carsonrobles/fpga-guitar-pedal/src/rtl/top.sv

`include "defaults.svh"
`include "sample_pkg.svh"

module top (
  input  wire        FPGA_CLK_100,
  input  wire        FPGA_RST_N,

  input  wire [15:0] SW,                  // switches
  output wire [15:0] LED,                 // LEDs
  output wire [ 2:0] RGB_L,               // RGB LEDs
  output wire [ 2:0] RGB_R,

  output wire        JA_MCLK_TX,          // PMOD I2S ports
  output wire        JA_LRCK_TX,
  output wire        JA_SCLK_TX,
  output wire        JA_SDO_TX,
  output wire        JA_MCLK_RX,
  output wire        JA_LRCK_RX,
  output wire        JA_SCLK_RX,
  input  wire        JA_SDI_RX
);


  wire mclk;

  mclk_gen mclk_gen_i (
    .clk  (FPGA_CLK_100),
    .rst  (~FPGA_RST_N),
    .mclk (mclk)
  );


  // synchronize external reset button to mclk domain
  wire rst;

  sync #(
    .NUM_FF     (2),
    .INIT_VALUE (0)
  ) sync_rst_i (
    .clk   (mclk),
    .rst   (0),
    .sig_i (~FPGA_RST_N),
    .sig_o (rst)
  );


  wire lrck;
  wire sclk;

  sample_pkg::sample_t rx_data;
  wire                 rx_vld;
  sample_pkg::sample_t tx_data;
  wire                 tx_vld;

  // i2s communication
  i2s i2s_i (
    .mclk    (mclk),
    .rst     (rst),
    .rx_data (rx_data),
    .rx_vld  (rx_vld),
    .tx_data (tx_data),
    .tx_vld  (tx_vld),
    .lrck    (lrck),
    .sclk    (sclk),
    .sdi     (JA_SDI_RX),
    .sdo     (JA_SDO_TX)
  );

  // assign PMOD clock outputs
  assign JA_MCLK_TX = mclk;
  assign JA_LRCK_TX = lrck;
  assign JA_SCLK_TX = sclk;
  assign JA_MCLK_RX = mclk;
  assign JA_LRCK_RX = lrck;
  assign JA_SCLK_RX = sclk;


  wire eff_en = 1;

  // effects pipe
  eff_pipe eff_pipe_i (
    .clk    (mclk),
    .rst    (rst),
    .en     (eff_en),
    .sel    (SW),
    .data_i (rx_data),
    .vld_i  (rx_vld),
    .data_o (tx_data),
    .vld_o  (tx_vld)
  );


  // leds follow switches
  assign LED = SW;

  // heartbeat LEDs
  rgb_drv rgb_drv_l_i (
    .clk  (FPGA_CLK_100),
    .rst  (~FPGA_RST_N),
    .mode (1),
    .red  (RGB_L[0]),
    .grn  (RGB_L[1]),
    .blu  (RGB_L[2])
  );

  assign RGB_R[0] = 0;
  assign RGB_R[1] = 0;
  assign RGB_R[2] = ~RGB_L[2];


endmodule
