carsonrobles/fpga-guitar-pedal/src/rtl/nco/cos_lut.sv

`include "defaults.svh"


module cos_lut #(
  parameter     FILE_NAME = "/home/carson/poly/fpga-guitar-pedal/fab/data/lut.hex",
  parameter int WIDTH     = 24,
  parameter int DEPTH     = 256
) (
  input  wire                      clk,
  input  wire                      rst,

  input  wire  [$clog2(DEPTH)-1:0] phi,

  output logic [        WIDTH-1:0] wav
);


  logic [WIDTH-1:0] lut [DEPTH];

  initial begin
    // read sinusoid data file into lut
    $readmemh(FILE_NAME, lut);
  end


  always_comb wav = lut[phi];


endmodule
