carsonrobles/fpga-guitar-pedal/src/ip/clk_wiz_ip/clk_wiz_ip_sim_netlist.v

// Copyright 1986-2018 Xilinx, Inc. All Rights Reserved.
// --------------------------------------------------------------------------------
// Tool Version: Vivado v.2018.3 (lin64) Build 2405991 Thu Dec  6 23:36:41 MST 2018
// Date        : Wed Apr 24 12:31:04 2019
// Host        : ubuntu running 64-bit Ubuntu 18.04.1 LTS
// Command     : write_verilog -force -mode funcsim
//               /home/carson/poly/fpga-guitar-pedal/src/ip/clk_wiz_ip/clk_wiz_ip_sim_netlist.v
// Design      : clk_wiz_ip
// Purpose     : This verilog netlist is a functional simulation representation of the design and should not be modified
//               or synthesized. This netlist cannot be used for SDF annotated simulation.
// Device      : xc7a100tcsg324-1
// --------------------------------------------------------------------------------
`timescale 1 ps / 1 ps

(* NotValidForBitStream *)
module clk_wiz_ip
   (clk_o,
    reset,
    locked,
    clk_i);
  output clk_o;
  input reset;
  output locked;
  input clk_i;

  (* IBUF_LOW_PWR *) wire clk_i;
  wire clk_o;
  wire locked;
  wire reset;

  clk_wiz_ip_clk_wiz_ip_clk_wiz inst
       (.clk_i(clk_i),
        .clk_o(clk_o),
        .locked(locked),
        .reset(reset));
endmodule

(* ORIG_REF_NAME = "clk_wiz_ip_clk_wiz" *) 
module clk_wiz_ip_clk_wiz_ip_clk_wiz
   (clk_o,
    reset,
    locked,
    clk_i);
  output clk_o;
  input reset;
  output locked;
  input clk_i;

  wire clk_i;
  wire clk_i_clk_wiz_ip;
  wire clk_o;
  wire clk_o_clk_wiz_ip;
  wire clkfbout_buf_clk_wiz_ip;
  wire clkfbout_clk_wiz_ip;
  wire locked;
  wire reset;
  wire NLW_plle2_adv_inst_CLKOUT1_UNCONNECTED;
  wire NLW_plle2_adv_inst_CLKOUT2_UNCONNECTED;
  wire NLW_plle2_adv_inst_CLKOUT3_UNCONNECTED;
  wire NLW_plle2_adv_inst_CLKOUT4_UNCONNECTED;
  wire NLW_plle2_adv_inst_CLKOUT5_UNCONNECTED;
  wire NLW_plle2_adv_inst_DRDY_UNCONNECTED;
  wire [15:0]NLW_plle2_adv_inst_DO_UNCONNECTED;

  (* BOX_TYPE = "PRIMITIVE" *) 
  BUFG clkf_buf
       (.I(clkfbout_clk_wiz_ip),
        .O(clkfbout_buf_clk_wiz_ip));
  (* BOX_TYPE = "PRIMITIVE" *) 
  (* CAPACITANCE = "DONT_CARE" *) 
  (* IBUF_DELAY_VALUE = "0" *) 
  (* IFD_DELAY_VALUE = "AUTO" *) 
  IBUF #(
    .IOSTANDARD("DEFAULT")) 
    clkin1_ibufg
       (.I(clk_i),
        .O(clk_i_clk_wiz_ip));
  (* BOX_TYPE = "PRIMITIVE" *) 
  BUFG clkout1_buf
       (.I(clk_o_clk_wiz_ip),
        .O(clk_o));
  (* BOX_TYPE = "PRIMITIVE" *) 
  PLLE2_ADV #(
    .BANDWIDTH("OPTIMIZED"),
    .CLKFBOUT_MULT(14),
    .CLKFBOUT_PHASE(0.000000),
    .CLKIN1_PERIOD(10.000000),
    .CLKIN2_PERIOD(0.000000),
    .CLKOUT0_DIVIDE(62),
    .CLKOUT0_DUTY_CYCLE(0.500000),
    .CLKOUT0_PHASE(0.000000),
    .CLKOUT1_DIVIDE(1),
    .CLKOUT1_DUTY_CYCLE(0.500000),
    .CLKOUT1_PHASE(0.000000),
    .CLKOUT2_DIVIDE(1),
    .CLKOUT2_DUTY_CYCLE(0.500000),
    .CLKOUT2_PHASE(0.000000),
    .CLKOUT3_DIVIDE(1),
    .CLKOUT3_DUTY_CYCLE(0.500000),
    .CLKOUT3_PHASE(0.000000),
    .CLKOUT4_DIVIDE(1),
    .CLKOUT4_DUTY_CYCLE(0.500000),
    .CLKOUT4_PHASE(0.000000),
    .CLKOUT5_DIVIDE(1),
    .CLKOUT5_DUTY_CYCLE(0.500000),
    .CLKOUT5_PHASE(0.000000),
    .COMPENSATION("ZHOLD"),
    .DIVCLK_DIVIDE(1),
    .IS_CLKINSEL_INVERTED(1'b0),
    .IS_PWRDWN_INVERTED(1'b0),
    .IS_RST_INVERTED(1'b0),
    .REF_JITTER1(0.010000),
    .REF_JITTER2(0.010000),
    .STARTUP_WAIT("FALSE")) 
    plle2_adv_inst
       (.CLKFBIN(clkfbout_buf_clk_wiz_ip),
        .CLKFBOUT(clkfbout_clk_wiz_ip),
        .CLKIN1(clk_i_clk_wiz_ip),
        .CLKIN2(1'b0),
        .CLKINSEL(1'b1),
        .CLKOUT0(clk_o_clk_wiz_ip),
        .CLKOUT1(NLW_plle2_adv_inst_CLKOUT1_UNCONNECTED),
        .CLKOUT2(NLW_plle2_adv_inst_CLKOUT2_UNCONNECTED),
        .CLKOUT3(NLW_plle2_adv_inst_CLKOUT3_UNCONNECTED),
        .CLKOUT4(NLW_plle2_adv_inst_CLKOUT4_UNCONNECTED),
        .CLKOUT5(NLW_plle2_adv_inst_CLKOUT5_UNCONNECTED),
        .DADDR({1'b0,1'b0,1'b0,1'b0,1'b0,1'b0,1'b0}),
        .DCLK(1'b0),
        .DEN(1'b0),
        .DI({1'b0,1'b0,1'b0,1'b0,1'b0,1'b0,1'b0,1'b0,1'b0,1'b0,1'b0,1'b0,1'b0,1'b0,1'b0,1'b0}),
        .DO(NLW_plle2_adv_inst_DO_UNCONNECTED[15:0]),
        .DRDY(NLW_plle2_adv_inst_DRDY_UNCONNECTED),
        .DWE(1'b0),
        .LOCKED(locked),
        .PWRDWN(1'b0),
        .RST(reset));
endmodule
`ifndef GLBL
`define GLBL
`timescale  1 ps / 1 ps

module glbl ();

    parameter ROC_WIDTH = 100000;
    parameter TOC_WIDTH = 0;

//--------   STARTUP Globals --------------
    wire GSR;
    wire GTS;
    wire GWE;
    wire PRLD;
    tri1 p_up_tmp;
    tri (weak1, strong0) PLL_LOCKG = p_up_tmp;

    wire PROGB_GLBL;
    wire CCLKO_GLBL;
    wire FCSBO_GLBL;
    wire [3:0] DO_GLBL;
    wire [3:0] DI_GLBL;
   
    reg GSR_int;
    reg GTS_int;
    reg PRLD_int;

//--------   JTAG Globals --------------
    wire JTAG_TDO_GLBL;
    wire JTAG_TCK_GLBL;
    wire JTAG_TDI_GLBL;
    wire JTAG_TMS_GLBL;
    wire JTAG_TRST_GLBL;

    reg JTAG_CAPTURE_GLBL;
    reg JTAG_RESET_GLBL;
    reg JTAG_SHIFT_GLBL;
    reg JTAG_UPDATE_GLBL;
    reg JTAG_RUNTEST_GLBL;

    reg JTAG_SEL1_GLBL = 0;
    reg JTAG_SEL2_GLBL = 0 ;
    reg JTAG_SEL3_GLBL = 0;
    reg JTAG_SEL4_GLBL = 0;

    reg JTAG_USER_TDO1_GLBL = 1'bz;
    reg JTAG_USER_TDO2_GLBL = 1'bz;
    reg JTAG_USER_TDO3_GLBL = 1'bz;
    reg JTAG_USER_TDO4_GLBL = 1'bz;

    assign (strong1, weak0) GSR = GSR_int;
    assign (strong1, weak0) GTS = GTS_int;
    assign (weak1, weak0) PRLD = PRLD_int;

    initial begin
	GSR_int = 1'b1;
	PRLD_int = 1'b1;
	#(ROC_WIDTH)
	GSR_int = 1'b0;
	PRLD_int = 1'b0;
    end

    initial begin
	GTS_int = 1'b1;
	#(TOC_WIDTH)
	GTS_int = 1'b0;
    end

endmodule
`endif
