carsonrobles/fpga-guitar-pedal/src/ip/clk_wiz_ip/clk_wiz_ip_sim_netlist.vhdl

-- Copyright 1986-2018 Xilinx, Inc. All Rights Reserved.
-- --------------------------------------------------------------------------------
-- Tool Version: Vivado v.2018.3 (lin64) Build 2405991 Thu Dec  6 23:36:41 MST 2018
-- Date        : Wed Apr 24 12:31:04 2019
-- Host        : ubuntu running 64-bit Ubuntu 18.04.1 LTS
-- Command     : write_vhdl -force -mode funcsim
--               /home/carson/poly/fpga-guitar-pedal/src/ip/clk_wiz_ip/clk_wiz_ip_sim_netlist.vhdl
-- Design      : clk_wiz_ip
-- Purpose     : This VHDL netlist is a functional simulation representation of the design and should not be modified or
--               synthesized. This netlist cannot be used for SDF annotated simulation.
-- Device      : xc7a100tcsg324-1
-- --------------------------------------------------------------------------------
library IEEE;
use IEEE.STD_LOGIC_1164.ALL;
library UNISIM;
use UNISIM.VCOMPONENTS.ALL;
entity clk_wiz_ip_clk_wiz_ip_clk_wiz is
  port (
    clk_o : out STD_LOGIC;
    reset : in STD_LOGIC;
    locked : out STD_LOGIC;
    clk_i : in STD_LOGIC
  );
  attribute ORIG_REF_NAME : string;
  attribute ORIG_REF_NAME of clk_wiz_ip_clk_wiz_ip_clk_wiz : entity is "clk_wiz_ip_clk_wiz";
end clk_wiz_ip_clk_wiz_ip_clk_wiz;

architecture STRUCTURE of clk_wiz_ip_clk_wiz_ip_clk_wiz is
  signal clk_i_clk_wiz_ip : STD_LOGIC;
  signal clk_o_clk_wiz_ip : STD_LOGIC;
  signal clkfbout_buf_clk_wiz_ip : STD_LOGIC;
  signal clkfbout_clk_wiz_ip : STD_LOGIC;
  signal NLW_plle2_adv_inst_CLKOUT1_UNCONNECTED : STD_LOGIC;
  signal NLW_plle2_adv_inst_CLKOUT2_UNCONNECTED : STD_LOGIC;
  signal NLW_plle2_adv_inst_CLKOUT3_UNCONNECTED : STD_LOGIC;
  signal NLW_plle2_adv_inst_CLKOUT4_UNCONNECTED : STD_LOGIC;
  signal NLW_plle2_adv_inst_CLKOUT5_UNCONNECTED : STD_LOGIC;
  signal NLW_plle2_adv_inst_DRDY_UNCONNECTED : STD_LOGIC;
  signal NLW_plle2_adv_inst_DO_UNCONNECTED : STD_LOGIC_VECTOR ( 15 downto 0 );
  attribute BOX_TYPE : string;
  attribute BOX_TYPE of clkf_buf : label is "PRIMITIVE";
  attribute BOX_TYPE of clkin1_ibufg : label is "PRIMITIVE";
  attribute CAPACITANCE : string;
  attribute CAPACITANCE of clkin1_ibufg : label is "DONT_CARE";
  attribute IBUF_DELAY_VALUE : string;
  attribute IBUF_DELAY_VALUE of clkin1_ibufg : label is "0";
  attribute IFD_DELAY_VALUE : string;
  attribute IFD_DELAY_VALUE of clkin1_ibufg : label is "AUTO";
  attribute BOX_TYPE of clkout1_buf : label is "PRIMITIVE";
  attribute BOX_TYPE of plle2_adv_inst : label is "PRIMITIVE";
begin
clkf_buf: unisim.vcomponents.BUFG
     port map (
      I => clkfbout_clk_wiz_ip,
      O => clkfbout_buf_clk_wiz_ip
    );
clkin1_ibufg: unisim.vcomponents.IBUF
    generic map(
      IOSTANDARD => "DEFAULT"
    )
        port map (
      I => clk_i,
      O => clk_i_clk_wiz_ip
    );
clkout1_buf: unisim.vcomponents.BUFG
     port map (
      I => clk_o_clk_wiz_ip,
      O => clk_o
    );
plle2_adv_inst: unisim.vcomponents.PLLE2_ADV
    generic map(
      BANDWIDTH => "OPTIMIZED",
      CLKFBOUT_MULT => 14,
      CLKFBOUT_PHASE => 0.000000,
      CLKIN1_PERIOD => 10.000000,
      CLKIN2_PERIOD => 0.000000,
      CLKOUT0_DIVIDE => 62,
      CLKOUT0_DUTY_CYCLE => 0.500000,
      CLKOUT0_PHASE => 0.000000,
      CLKOUT1_DIVIDE => 1,
      CLKOUT1_DUTY_CYCLE => 0.500000,
      CLKOUT1_PHASE => 0.000000,
      CLKOUT2_DIVIDE => 1,
      CLKOUT2_DUTY_CYCLE => 0.500000,
      CLKOUT2_PHASE => 0.000000,
      CLKOUT3_DIVIDE => 1,
      CLKOUT3_DUTY_CYCLE => 0.500000,
      CLKOUT3_PHASE => 0.000000,
      CLKOUT4_DIVIDE => 1,
      CLKOUT4_DUTY_CYCLE => 0.500000,
      CLKOUT4_PHASE => 0.000000,
      CLKOUT5_DIVIDE => 1,
      CLKOUT5_DUTY_CYCLE => 0.500000,
      CLKOUT5_PHASE => 0.000000,
      COMPENSATION => "ZHOLD",
      DIVCLK_DIVIDE => 1,
      IS_CLKINSEL_INVERTED => '0',
      IS_PWRDWN_INVERTED => '0',
      IS_RST_INVERTED => '0',
      REF_JITTER1 => 0.010000,
      REF_JITTER2 => 0.010000,
      STARTUP_WAIT => "FALSE"
    )
        port map (
      CLKFBIN => clkfbout_buf_clk_wiz_ip,
      CLKFBOUT => clkfbout_clk_wiz_ip,
      CLKIN1 => clk_i_clk_wiz_ip,
      CLKIN2 => '0',
      CLKINSEL => '1',
      CLKOUT0 => clk_o_clk_wiz_ip,
      CLKOUT1 => NLW_plle2_adv_inst_CLKOUT1_UNCONNECTED,
      CLKOUT2 => NLW_plle2_adv_inst_CLKOUT2_UNCONNECTED,
      CLKOUT3 => NLW_plle2_adv_inst_CLKOUT3_UNCONNECTED,
      CLKOUT4 => NLW_plle2_adv_inst_CLKOUT4_UNCONNECTED,
      CLKOUT5 => NLW_plle2_adv_inst_CLKOUT5_UNCONNECTED,
      DADDR(6 downto 0) => B"0000000",
      DCLK => '0',
      DEN => '0',
      DI(15 downto 0) => B"0000000000000000",
      DO(15 downto 0) => NLW_plle2_adv_inst_DO_UNCONNECTED(15 downto 0),
      DRDY => NLW_plle2_adv_inst_DRDY_UNCONNECTED,
      DWE => '0',
      LOCKED => locked,
      PWRDWN => '0',
      RST => reset
    );
end STRUCTURE;
library IEEE;
use IEEE.STD_LOGIC_1164.ALL;
library UNISIM;
use UNISIM.VCOMPONENTS.ALL;
entity clk_wiz_ip is
  port (
    clk_o : out STD_LOGIC;
    reset : in STD_LOGIC;
    locked : out STD_LOGIC;
    clk_i : in STD_LOGIC
  );
  attribute NotValidForBitStream : boolean;
  attribute NotValidForBitStream of clk_wiz_ip : entity is true;
end clk_wiz_ip;

architecture STRUCTURE of clk_wiz_ip is
begin
inst: entity work.clk_wiz_ip_clk_wiz_ip_clk_wiz
     port map (
      clk_i => clk_i,
      clk_o => clk_o,
      locked => locked,
      reset => reset
    );
end STRUCTURE;
