carsonrobles/fpga-guitar-pedal/src/sim/eff/del_fifo_tb.sv

`timescale 1ns / 1ps
`default_nettype none

module del_fifo_tb;


  logic        clk     =  0;
  logic        rst     =  0;

  logic        en      =  0;

  logic [23:0] data_i  =  1;
  logic        vld_blk =  0;
  wire         vld_i;

  wire  [23:0] data_o;

  del_fifo #(
    .DATA_WIDTH (24),
    .FIFO_DEPTH (4)
  ) dut (
    .clk    (clk),
    .rst    (rst),
    .en     (en),
    .data_i (data_i),
    .vld_i  (vld_i & ~vld_blk),
    .data_o (data_o)
  );


  always_latch clk <= #5 ~clk;


  logic [2:0] cnt = '0;

  always_ff @ (posedge clk) begin
    cnt <= cnt + 1;
  end


  // increment incoming data every 8 clocks and make valid
  always_ff @ (posedge clk) begin
    data_i <= data_i + &cnt;
  end

  assign vld_i = &cnt;


  initial begin
    // initial setup: /rst, en
    @ (posedge clk);
    rst     <= 0;
    en      <= 1;
    vld_blk <= 0;

    // test blocking valid for a few clock cycles, leaving data incrementing
    repeat (70) @ (posedge clk);
    vld_blk <= 1;
    repeat (70) @ (posedge clk);
    vld_blk <= 0;

    // test dropping en, keeping valid and data running
    repeat (70) @ (posedge clk);
    en <= 0;
    repeat (70) @ (posedge clk);
    en <= 1;

    // test reset
    repeat (70) @ (posedge clk);
    rst <= 1;
    repeat (10) @ (posedge clk);
    rst <= 0;
  end


endmodule
